kanishkaIG/SAR-Beacon/Screenshots/IMG_4741.JPG

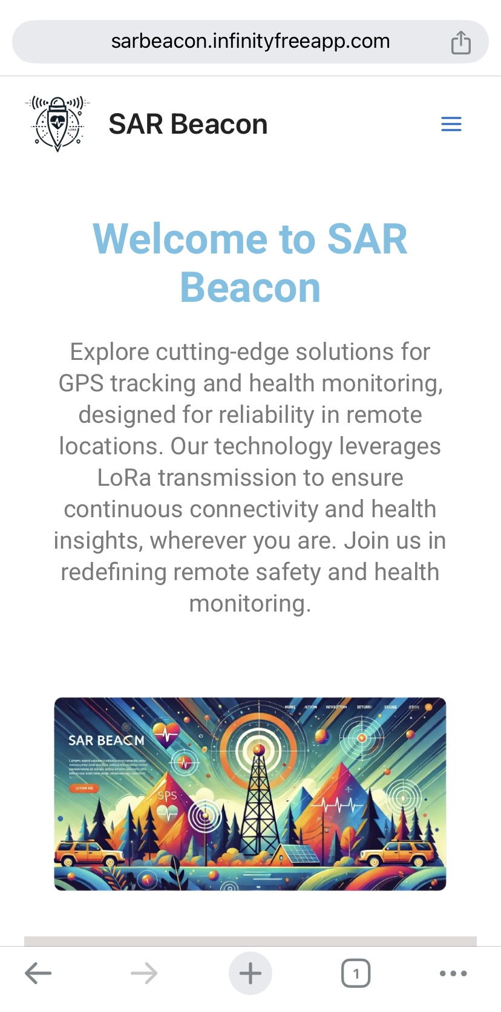
Screenshots/IMG_4741.JPG
