kanishkaIG/SAR-Beacon/Screenshots/IMG_4743.JPG

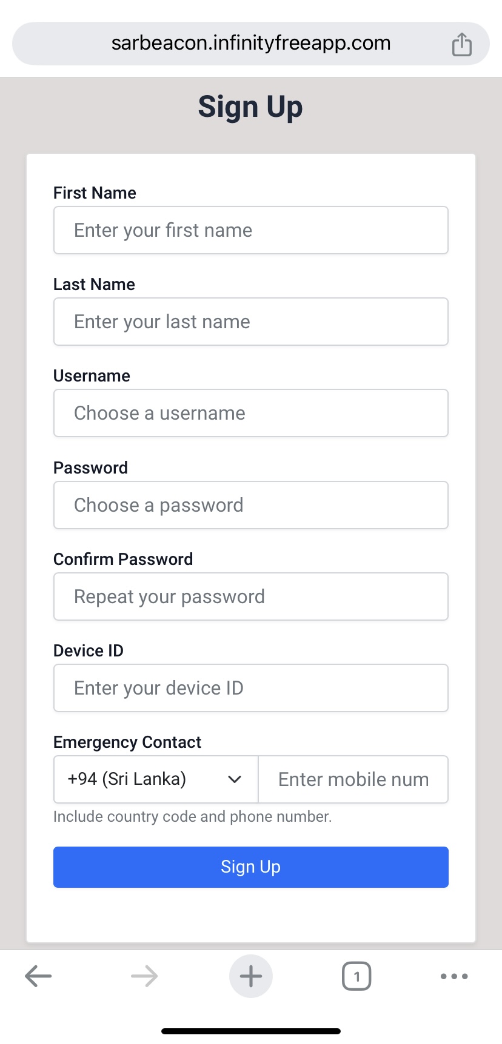
Screenshots/IMG_4743.JPG
