kanishkaIG/SAR-Beacon/Screenshots/IMG_4744.JPG

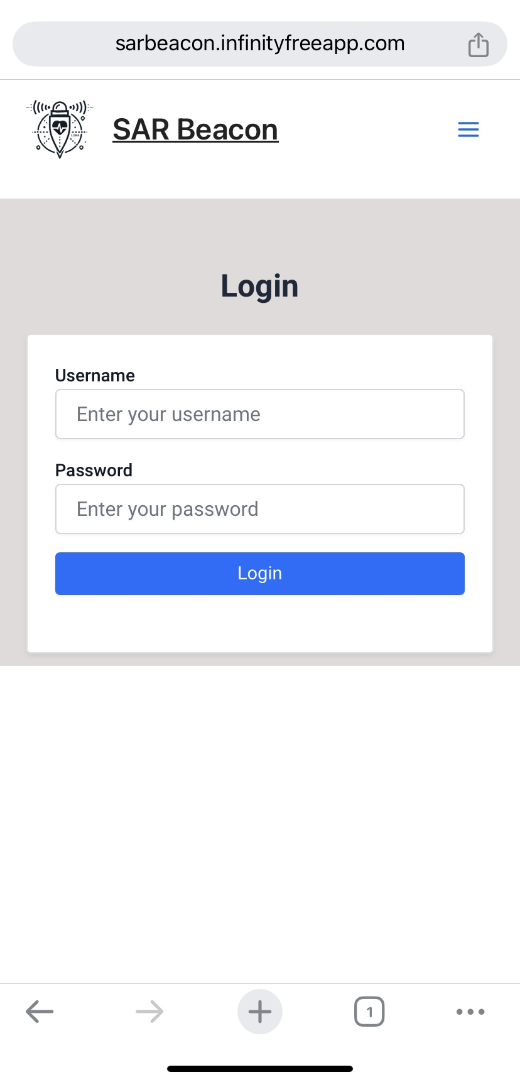
Screenshots/IMG_4744.JPG
