kanishkaIG/SAR-Beacon/Screenshots/IMG_4745.JPG

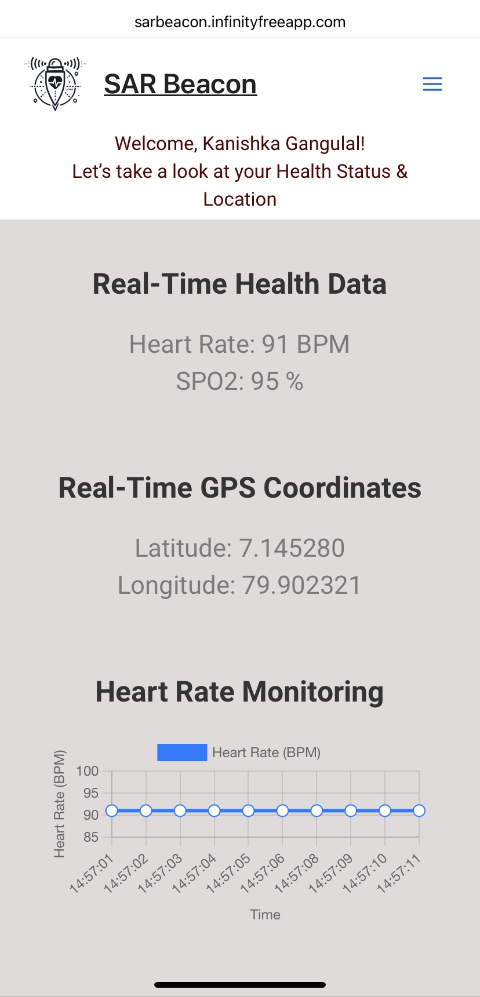
Screenshots/IMG_4745.JPG
