kanishkaIG/SAR-Beacon/Screenshots/IMG_4746.JPG

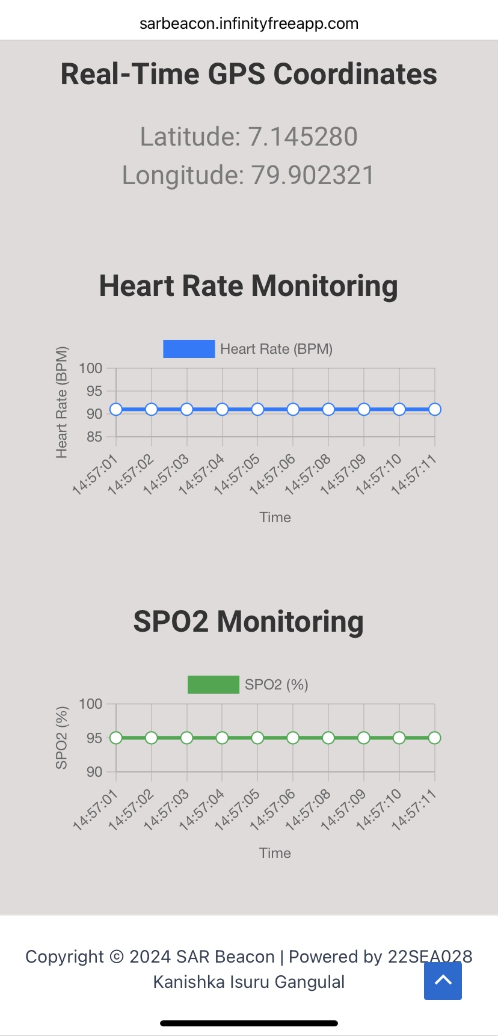
Screenshots/IMG_4746.JPG
