kanishkaIG/SAR-Beacon/Screenshots/IMG_4747.JPG

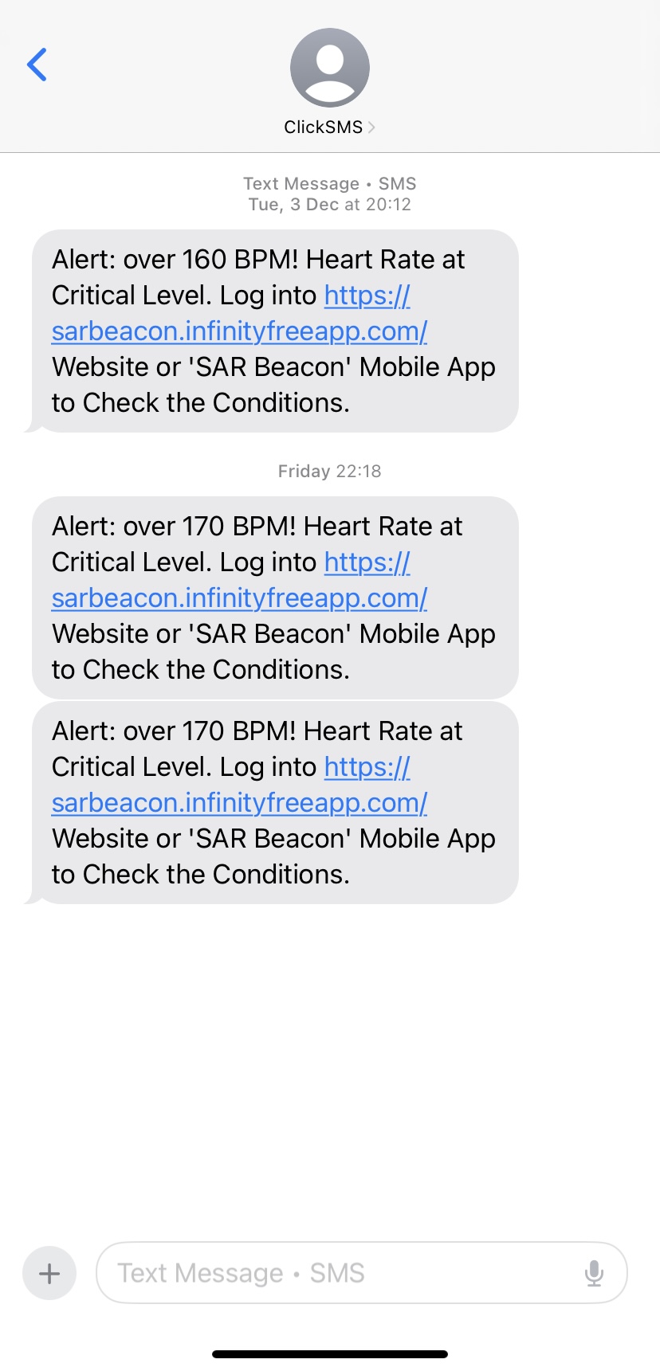
Screenshots/IMG_4747.JPG
