kanishkaIG/SAR-Beacon/Screenshots/IMG_4816.JPG

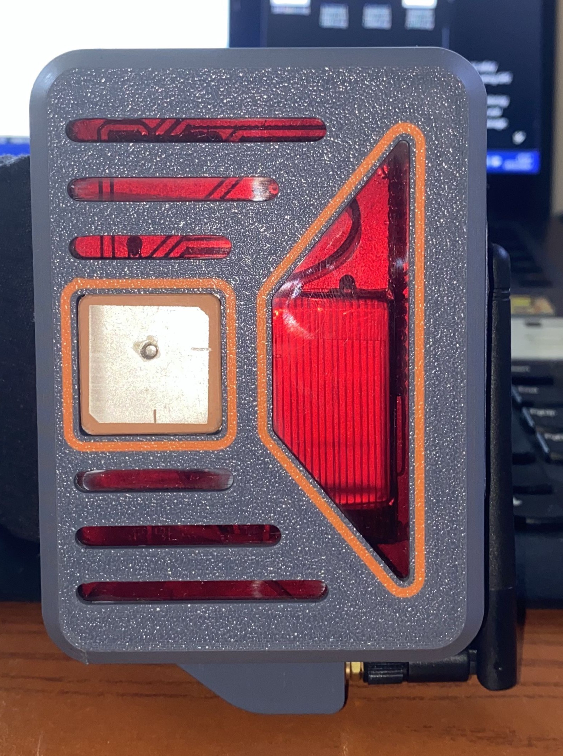
Screenshots/IMG_4816.JPG
