kanishkaIG/SAR-Beacon/Screenshots/IMG_4818.JPG

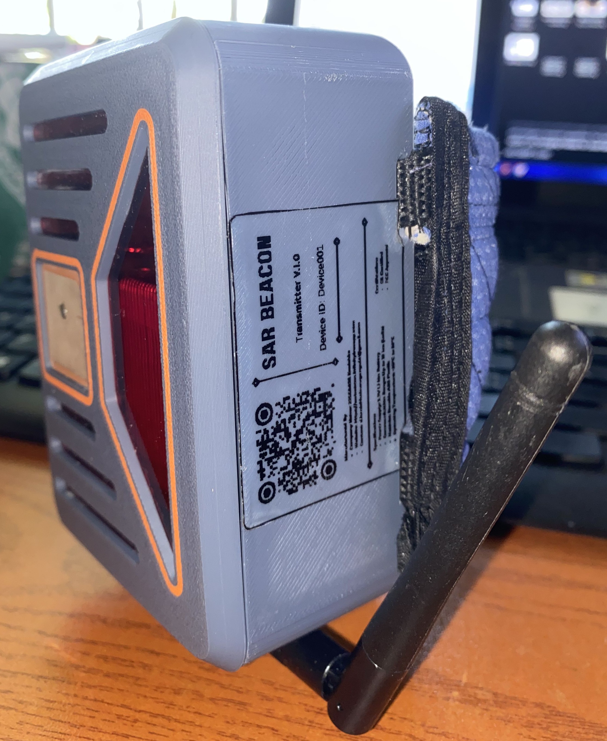
Screenshots/IMG_4818.JPG
