kanishkaIG/SAR-Beacon/Screenshots/IMG_4819.JPG

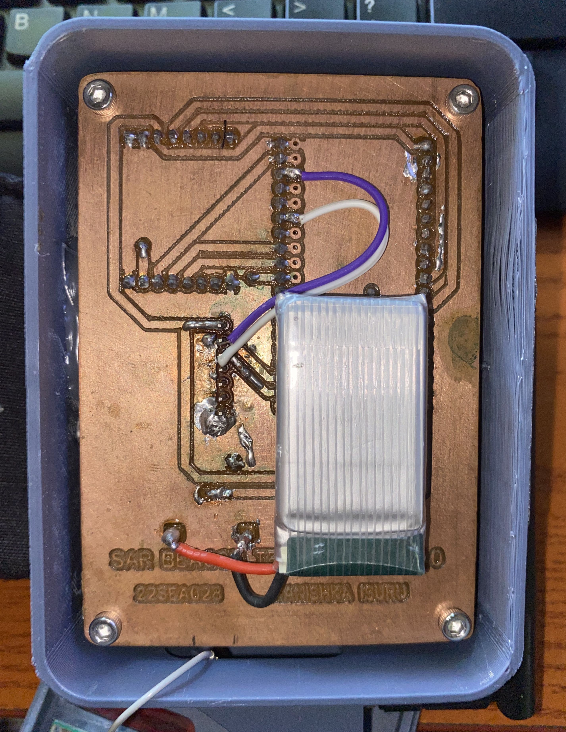
Screenshots/IMG_4819.JPG
