kanishkaIG/SAR-Beacon/Screenshots/IMG_4822.JPG

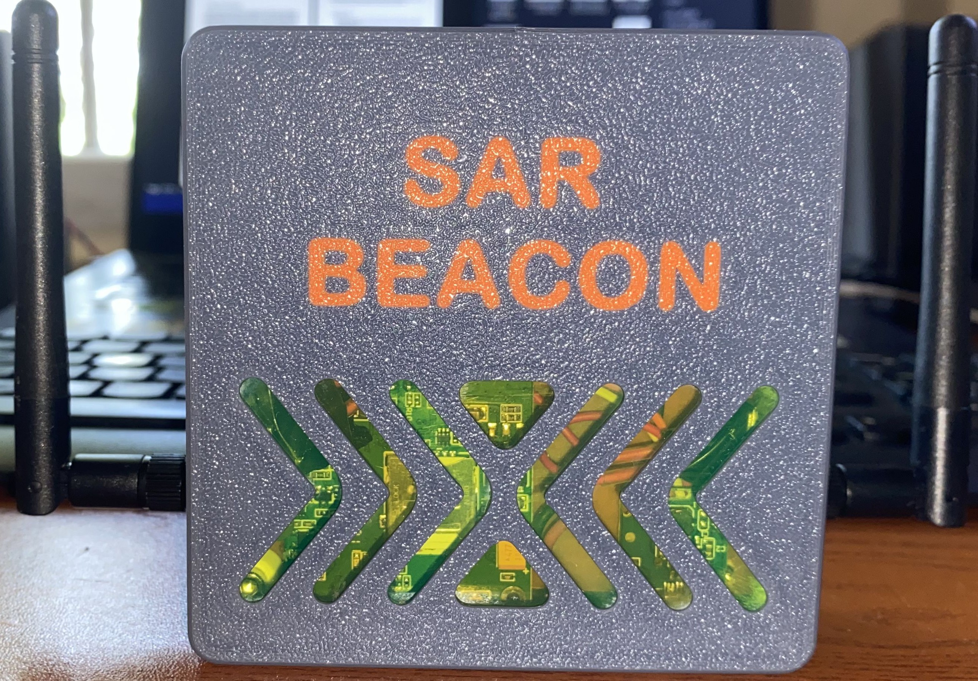
Screenshots/IMG_4822.JPG
