kanishkaIG/SAR-Beacon/Screenshots/IMG_4825.JPG

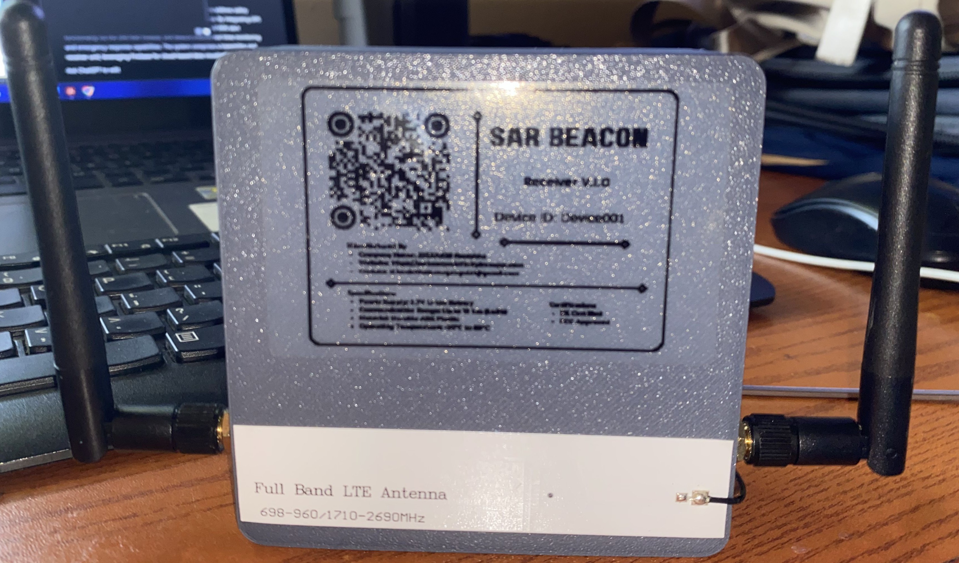
Screenshots/IMG_4825.JPG
