kanishkaIG/SAR-Beacon/Screenshots/IMG_4826.JPG

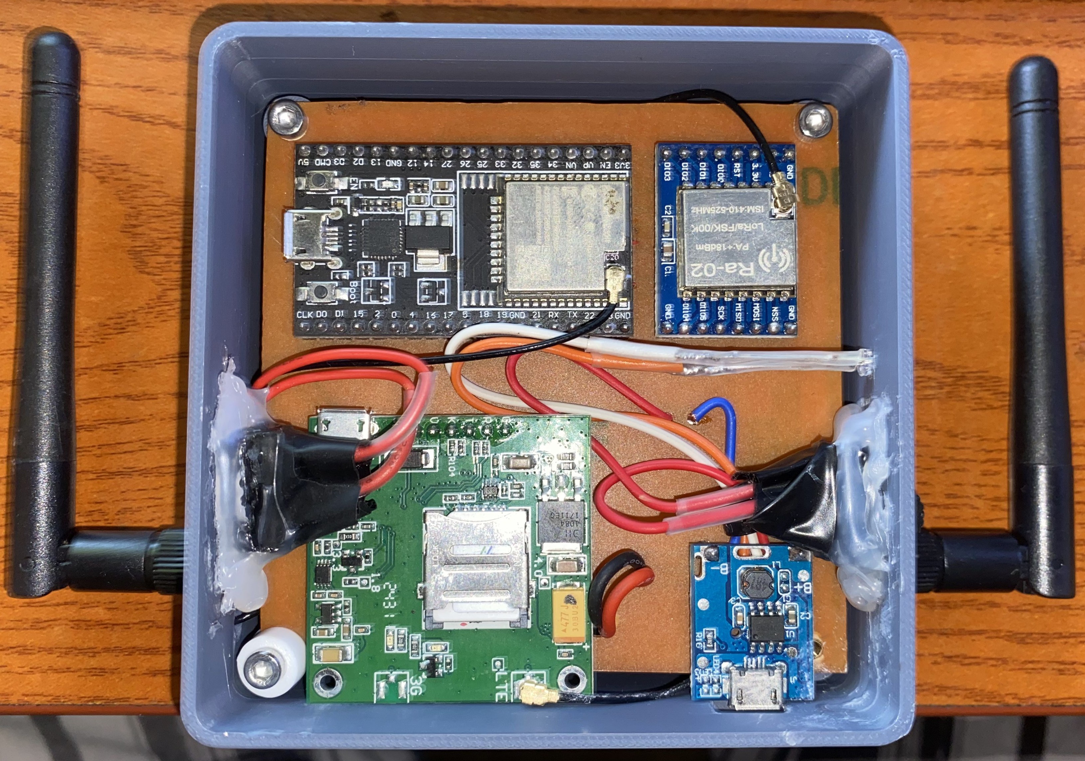
Screenshots/IMG_4826.JPG
