kanishkaIG/SAR-Beacon/Arduino_Code/LoRaReceiver.ino

#include <SPI.h>
#include <LoRa.h>


#define ss 5
#define rst 14
#define dio0 26


void setup() {
  Serial.begin(9600);
  while (!Serial);
  delay(500);
  Serial.println("LoRa Receiver");
  LoRa.setPins(ss, rst, dio0);
  if (!LoRa.begin(433E6)) {
    Serial.println("Starting LoRa failed!");
    while (1);
  }
  Serial.println("Starting LoRa failed!");
}

void loop() {
  // try to parse packet
  int packetSize = LoRa.parsePacket();
  if (packetSize) {
    // received a packet
    Serial.print("Received packet '");

    // read packet
    while (LoRa.available()) {
      Serial.print((char)LoRa.read());
    }

    // print RSSI of packet
    Serial.print("' with RSSI ");
    Serial.println(LoRa.packetRssi());
  }
}
