kanishkaIG/SAR-Beacon/Arduino_Code/LoRaSender.ino

#include <SPI.h>
#include <LoRa.h>

int counter = 0;

#define ss 5
#define rst 14
#define dio0 26

void setup() {
  Serial.begin(9600);
  while (!Serial);

  Serial.println("LoRa Sender");
  LoRa.setPins(ss, rst, dio0);
  if (!LoRa.begin(433E6)) {
    Serial.println("Starting LoRa failed!");
    while (1);
  }
}

void loop() {
  Serial.print("Sending packet: ");
  Serial.println(counter);

  // send packet
  LoRa.beginPacket();
  LoRa.print("hello ");
  LoRa.print(counter);
  LoRa.endPacket();

  counter++;

  delay(1000);
}
